mpboddie/TipsyBrewPourOver/TipsyBrew POR mkII/data/coffeeBeans.bmp

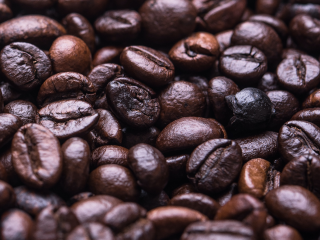
TipsyBrew POR mkII/data/coffeeBeans.bmp
