mpboddie/TipsyBrewPourOver/TipsyBrew POR mkII/src/icons.h

// 'TipsyBrew title', 300x62px
const unsigned char tipsyBrewTitle [] PROGMEM = {
  0x00, 0x00, 0x00, 0x00, 0x00, 0x00, 0x00, 0x00, 0x00, 0x00, 0x00, 0x00, 0x00, 0x00, 0x00, 0x00, 
  0x00, 0x00, 0x00, 0x00, 0x00, 0x00, 0x00, 0x00, 0x00, 0x00, 0x00, 0x00, 0x00, 0x00, 0x00, 0x00, 
  0x00, 0x00, 0x00, 0x00, 0x00, 0x00, 0x00, 0x00, 0x00, 0x00, 0x00, 0x00, 0x00, 0x00, 0x00, 0x00, 
  0x00, 0x00, 0x00, 0x00, 0x00, 0x00, 0x00, 0x00, 0x00, 0x00, 0x00, 0x00, 0x00, 0x00, 0x00, 0x00, 
  0x00, 0x00, 0x00, 0x00, 0x00, 0x00, 0x00, 0x00, 0x00, 0x00, 0x00, 0x00, 0x00, 0x00, 0x00, 0x00, 
  0x00, 0x00, 0x00, 0x00, 0x00, 0x00, 0x00, 0x00, 0x00, 0x00, 0x00, 0x00, 0x00, 0x00, 0x00, 0x00, 
  0x00, 0x00, 0x00, 0x00, 0x00, 0x00, 0x00, 0x00, 0x00, 0x00, 0x00, 0x00, 0x00, 0x00, 0x00, 0x00, 
  0x00, 0x00, 0x00, 0x7f, 0xff, 0xff, 0xf0, 0xff, 0x81, 0xff, 0xff, 0xff, 0x80, 0x3f, 0xff, 0xff, 
  0x81, 0xff, 0x00, 0x0f, 0xfc, 0x7f, 0xff, 0xff, 0xe0, 0x1f, 0xff, 0xff, 0xf8, 0x07, 0xff, 0xff, 
  0xf8, 0xff, 0x80, 0x3f, 0xc0, 0x3f, 0xf0, 0x00, 0x00, 0x7f, 0xff, 0xff, 0xf0, 0xff, 0x81, 0xff, 
  0xff, 0xff, 0xc0, 0x7f, 0xff, 0xff, 0xc1, 0xff, 0x80, 0x0f, 0xfc, 0x7f, 0xff, 0xff, 0xf0, 0x1f, 
  0xff, 0xff, 0xfc, 0x07, 0xff, 0xff, 0xf8, 0xff, 0x80, 0x7f, 0xc0, 0x3f, 0xe0, 0x00, 0x00, 0x7f, 
  0xff, 0xff, 0xf0, 0xff, 0x81, 0xff, 0xff, 0xff, 0xc0, 0xff, 0xff, 0xff, 0xe1, 0xff, 0x80, 0x0f, 
  0xfc, 0x7f, 0xff, 0xff, 0xf8, 0x1f, 0xff, 0xff, 0xfe, 0x07, 0xff, 0xff, 0xf8, 0xff, 0x80, 0x7f, 
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
	0x00, 0x3c, 0x00, 0x3c, 0x00, 0x00, 0x3c, 0x00, 0x3c, 0x00, 0x00, 0x1c, 0x00, 0x38, 0x00, 0x00, 
	0x1e, 0x00, 0x78, 0x00, 0x00, 0x1f, 0x81, 0xf8, 0x00, 0x00, 0x1f, 0xff, 0xf8, 0x00, 0x00, 0x0f, 
	0xff, 0xf0, 0x00, 0x00, 0x03, 0xff, 0xc0, 0x00
};
